teapotlaboratories/bwlr1b/docs/images/3d_bottom_cr2450.png

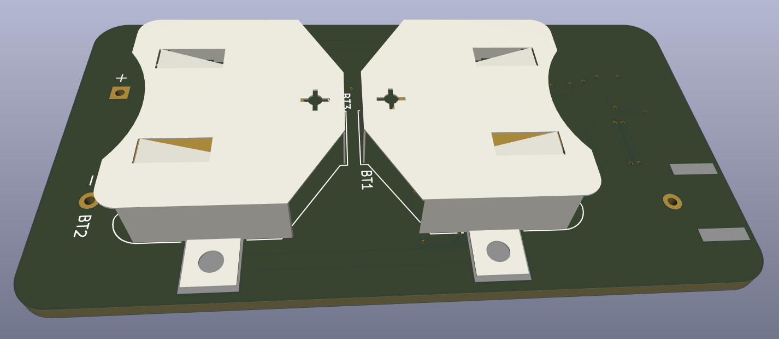
docs/images/3d_bottom_cr2450.png
