teapotlaboratories/bwlr1b/docs/images/aa_with_case.jpg

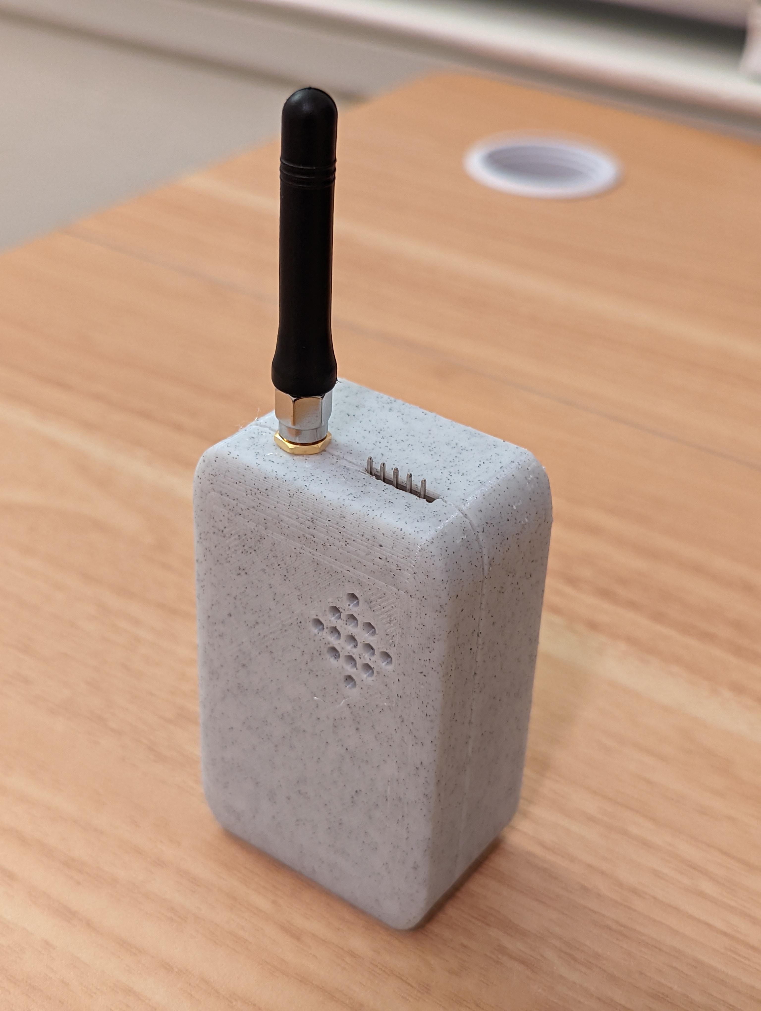
docs/images/aa_with_case.jpg
