teapotlaboratories/bwlr1b/docs/measurement/lora_ack.png

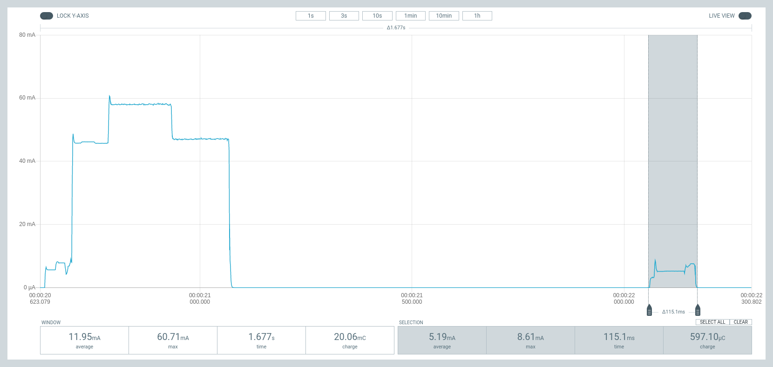
docs/measurement/lora_ack.png
